ZoeGet/CodexLight/Firmware/include/led.h

#ifndef CODEXLIGHT_LED_H
#define CODEXLIGHT_LED_H

#include <Arduino.h>

class LedController {
 public:
  void begin();

  void showRed();
  void showGreen();
  void showYellow();

  void allOff();

 private:
  void setBrightness(uint8_t brightness);
};

#endif  // CODEXLIGHT_LED_H
